BenZbor/My-Projects/CAD Files/SOLIDWORKS/Launcher Assembly.SLDASM

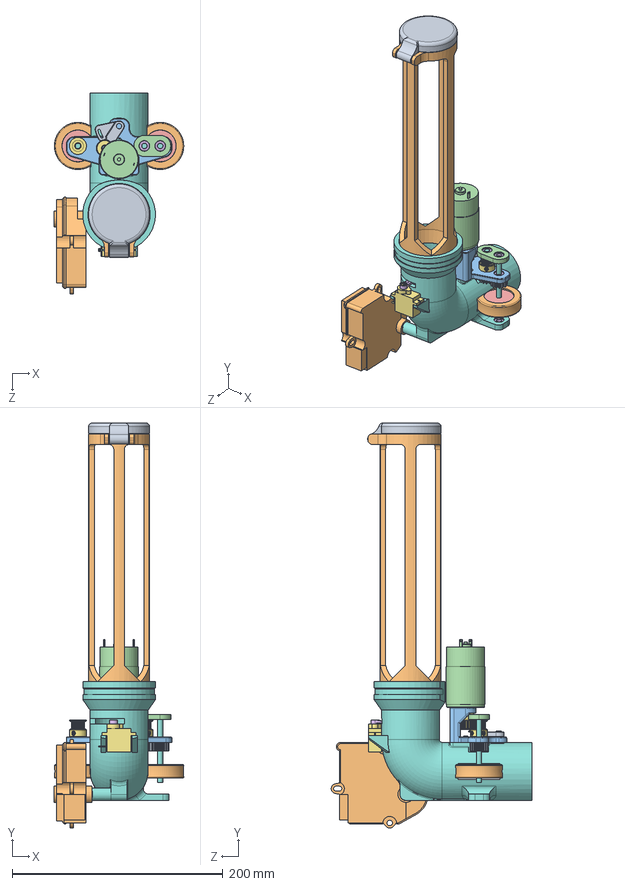
[picture p14: CAD file, 2025-08-28]
CAD Files/SOLIDWORKS/Launcher Assembly.SLDASM
122.8 x 383.9 x 190.2 mm
Magazine
MagazineTop
Feeder
SG90
SG90 Horn
Flywheel x 2
DC Motor
DC Motor Mount
Rotation Motor
Reversing Gear x 2
shaft x 5
GT2_06SWidth_20Num_5IDia_16HDia x 4
Bearing x 7
Coupler
Shaft support
Tensioner rod
Tire x 2
Tensioner V2
