BenZbor/My-Projects/CAD Files/SOLIDWORKS/Shaft support.SLDPRT

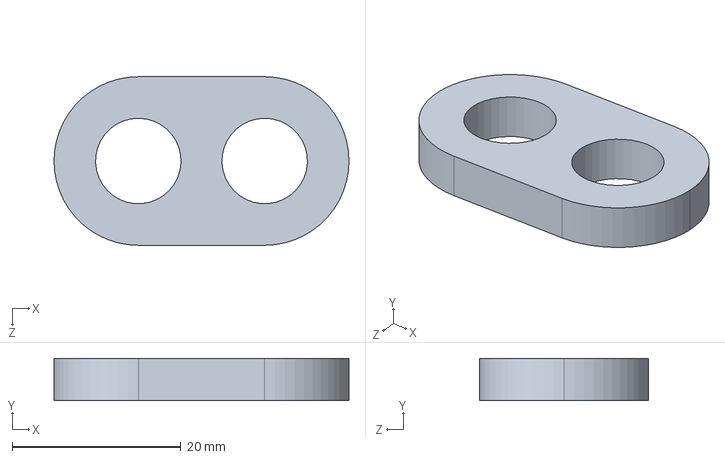
[picture p28: CAD file, 2025-08-28]
CAD Files/SOLIDWORKS/Shaft support.SLDPRT
35.0 x 5.00 x 20.0 mm
