BenZbor/My-Projects/CAD Files/SOLIDWORKS/Tank part/7.4V Battery.SLDPRT

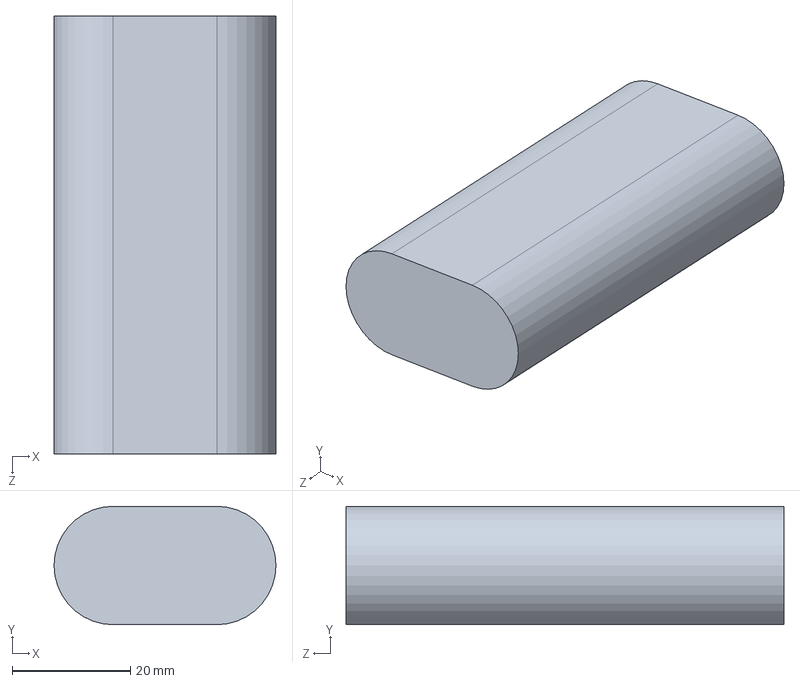
[picture p29: CAD file, 2025-08-28]
CAD Files/SOLIDWORKS/Tank part/7.4V Battery.SLDPRT
37.5 x 20.0 x 74.0 mm
