BenZbor/My-Projects/CAD Files/SOLIDWORKS/shaft.SLDPRT

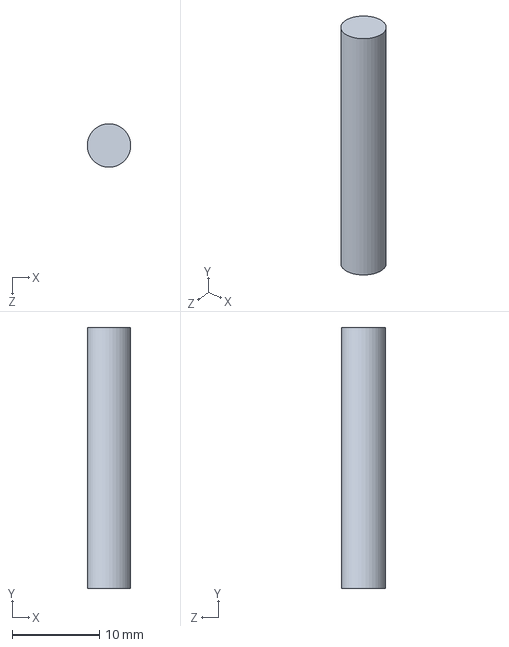
[picture p30: CAD file, 2025-08-28]
CAD Files/SOLIDWORKS/shaft.SLDPRT
4.98 x 30.0 x 5.00 mm
