BenZbor/My-Projects/CAD Files/SOLIDWORKS/Tire.SLDPRT

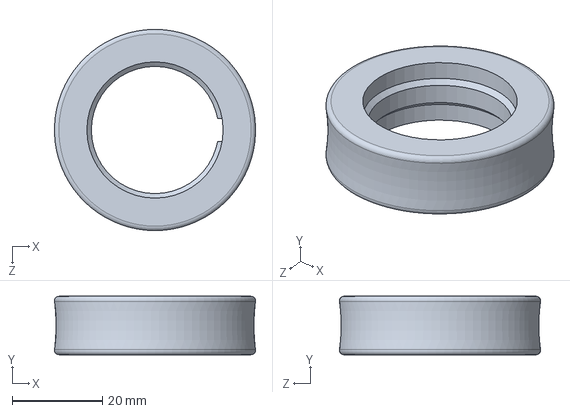
[picture p31: CAD file, 2025-08-28]
CAD Files/SOLIDWORKS/Tire.SLDPRT
44.6 x 13.0 x 44.7 mm
