BenZbor/My-Projects/CAD Files/SOLIDWORKS/Flywheel.SLDPRT

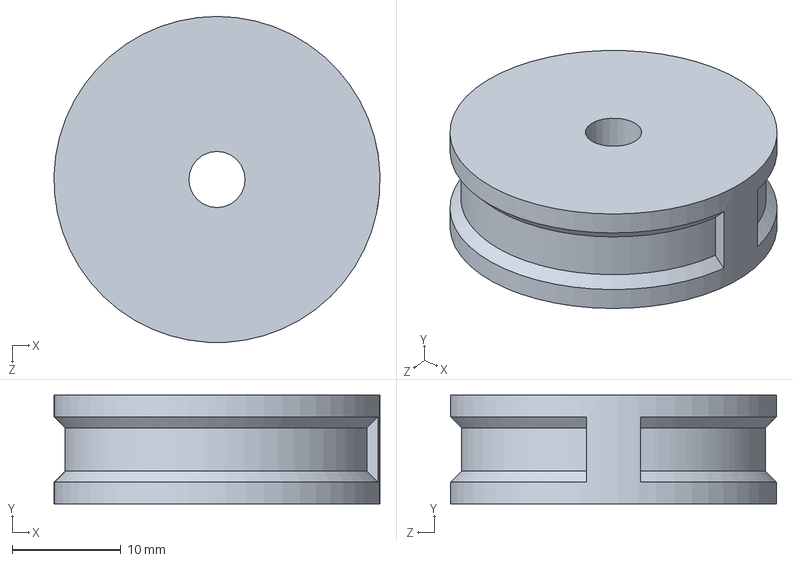
[picture p32: CAD file, 2025-08-28]
CAD Files/SOLIDWORKS/Flywheel.SLDPRT
30.0 x 10.0 x 30.0 mm
