BenZbor/My-Projects/CAD Files/SOLIDWORKS/DC Motor Mount.SLDPRT

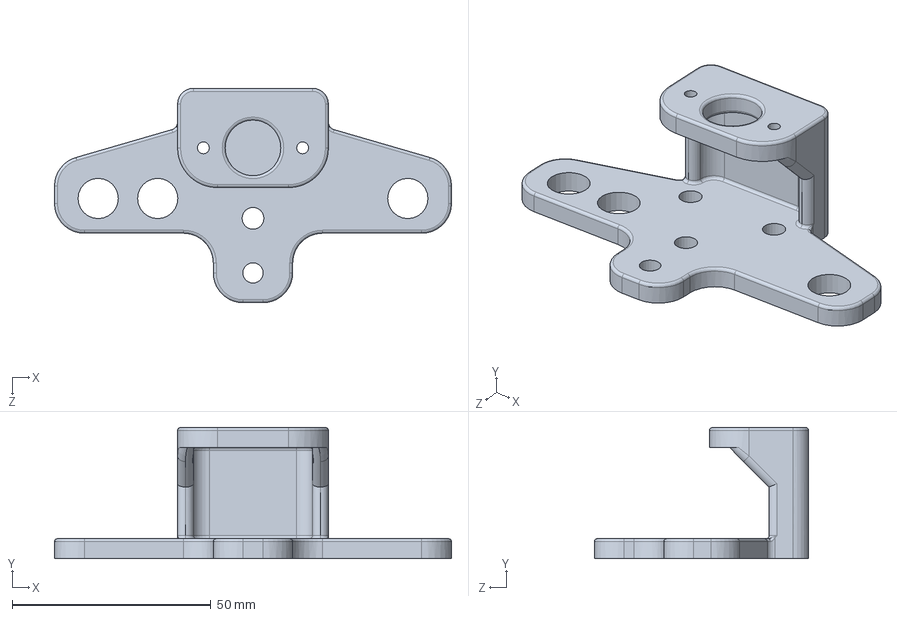
[picture p33: CAD file, 2025-08-28]
CAD Files/SOLIDWORKS/DC Motor Mount.SLDPRT
100.0 x 33.0 x 54.0 mm
