BenZbor/My-Projects/CAD Files/SOLIDWORKS/Feeder.SLDPRT

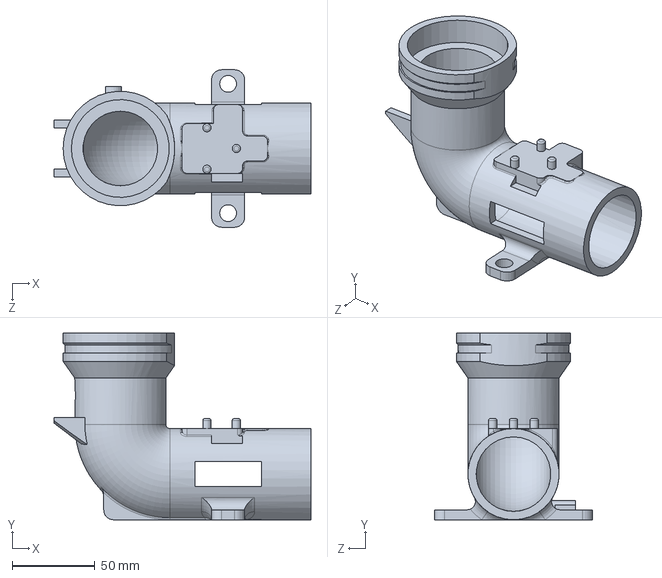
[picture p34: CAD file, 2025-08-28]
CAD Files/SOLIDWORKS/Feeder.SLDPRT
155.0 x 112.5 x 95.0 mm
