BenZbor/My-Projects/CAD Files/SOLIDWORKS/Reversing Gear.SLDPRT

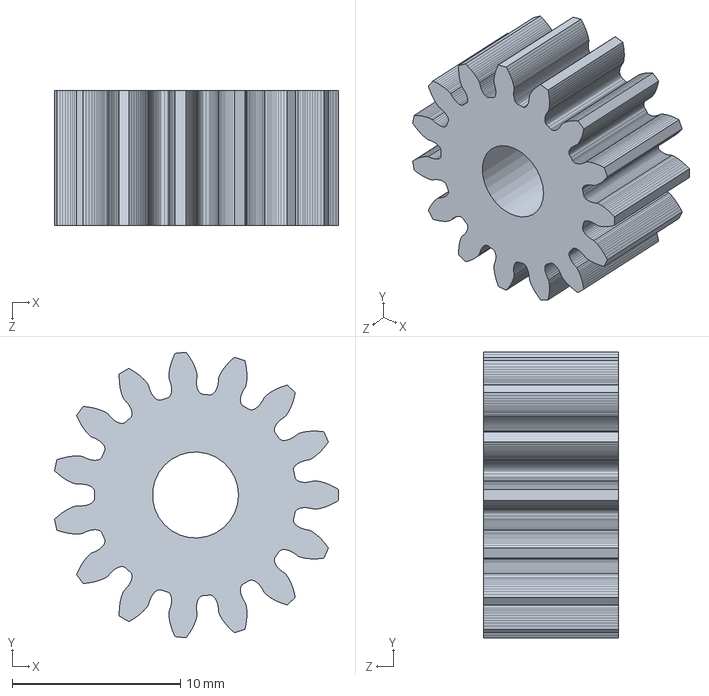
[picture p35: CAD file, 2025-08-28]
CAD Files/SOLIDWORKS/Reversing Gear.SLDPRT
16.9 x 17.0 x 8.00 mm
