BenZbor/My-Projects/CAD Files/SOLIDWORKS/Rotation Motor.SLDPRT

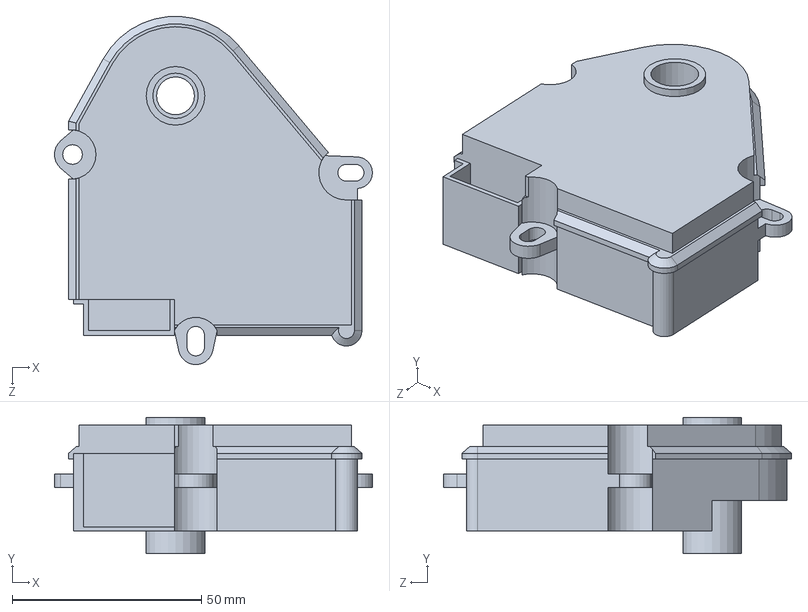
[picture p36: CAD file, 2025-08-28]
CAD Files/SOLIDWORKS/Rotation Motor.SLDPRT
84.0 x 36.0 x 91.9 mm
