BenZbor/My-Projects/CAD Files/SOLIDWORKS/Foam Ball.SLDPRT

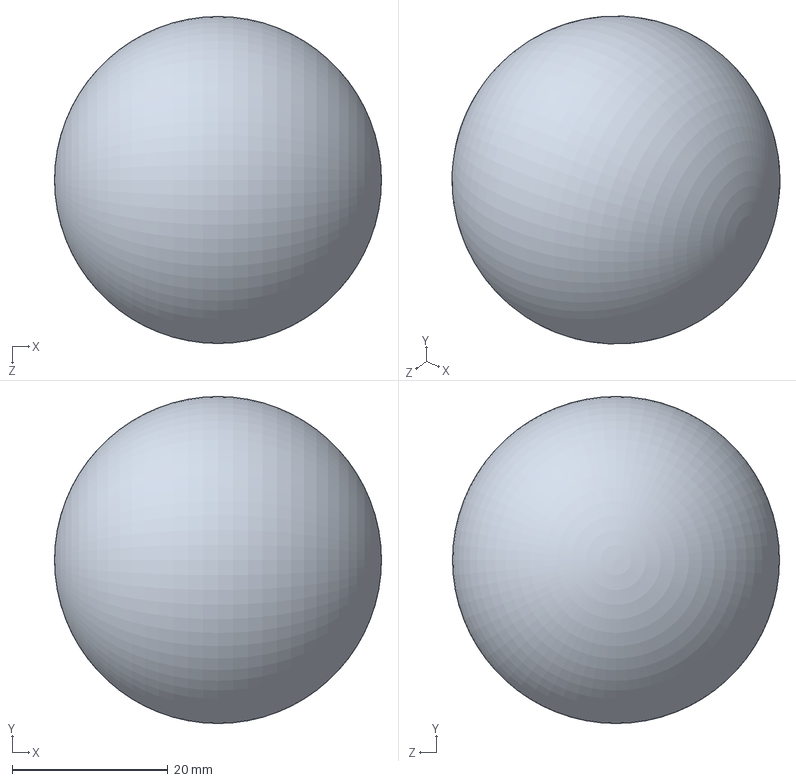
[picture p37: CAD file, 2025-08-28]
CAD Files/SOLIDWORKS/Foam Ball.SLDPRT
42.0 x 42.0 x 42.0 mm
