BenZbor/My-Projects/CAD Files/SOLIDWORKS/Magazine.SLDPRT

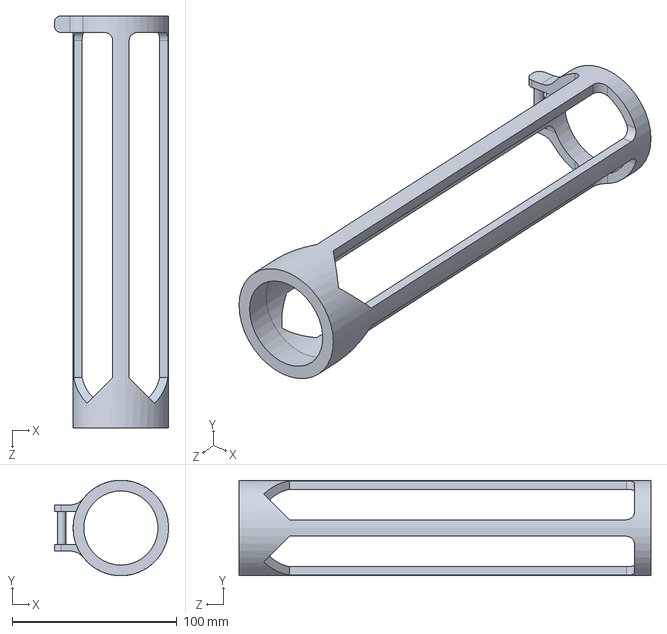
[picture p38: CAD file, 2025-08-28]
CAD Files/SOLIDWORKS/Magazine.SLDPRT
69.4 x 57.8 x 250.0 mm
