BenZbor/My-Projects/CAD Files/SOLIDWORKS/SG90 Horn.SLDPRT

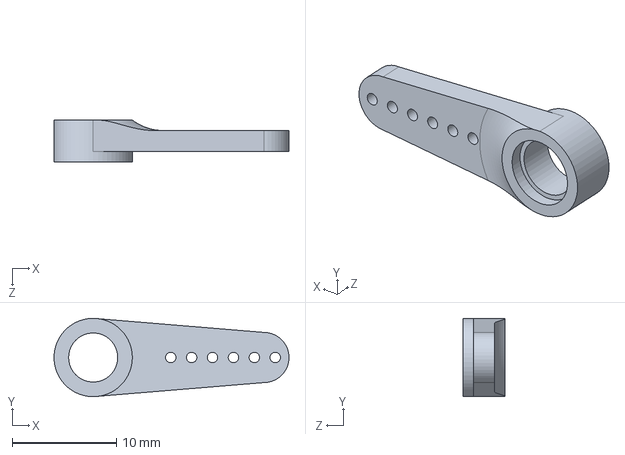
[picture p39: CAD file, 2025-08-28]
CAD Files/SOLIDWORKS/SG90 Horn.SLDPRT
22.5 x 7.50 x 4.00 mm
