BenZbor/My-Projects/CAD Files/SOLIDWORKS/SG90.SLDPRT

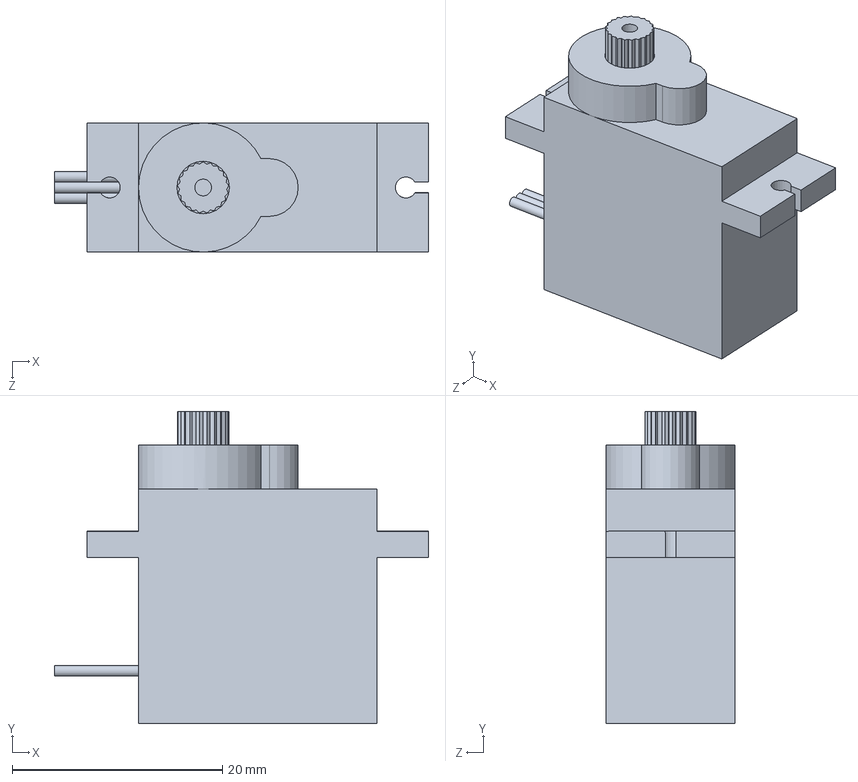
[picture p40: CAD file, 2025-08-28]
CAD Files/SOLIDWORKS/SG90.SLDPRT
35.6 x 29.7 x 12.3 mm
