BenZbor/My-Projects/CAD Files/SOLIDWORKS/Tensioner.SLDPRT

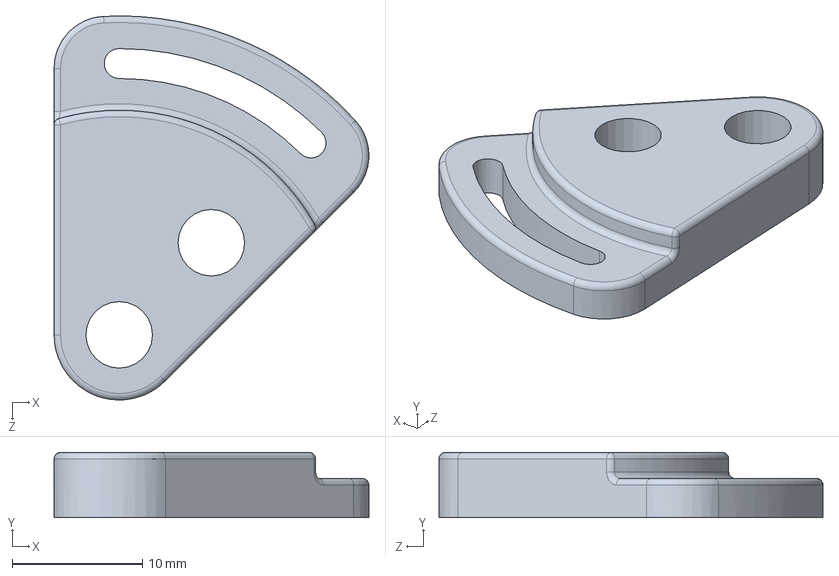
[picture p41: CAD file, 2025-08-28]
CAD Files/SOLIDWORKS/Tensioner.SLDPRT
24.2 x 5.00 x 29.5 mm
