BenZbor/My-Projects/CAD Files/SOLIDWORKS/Bearing.SLDPRT

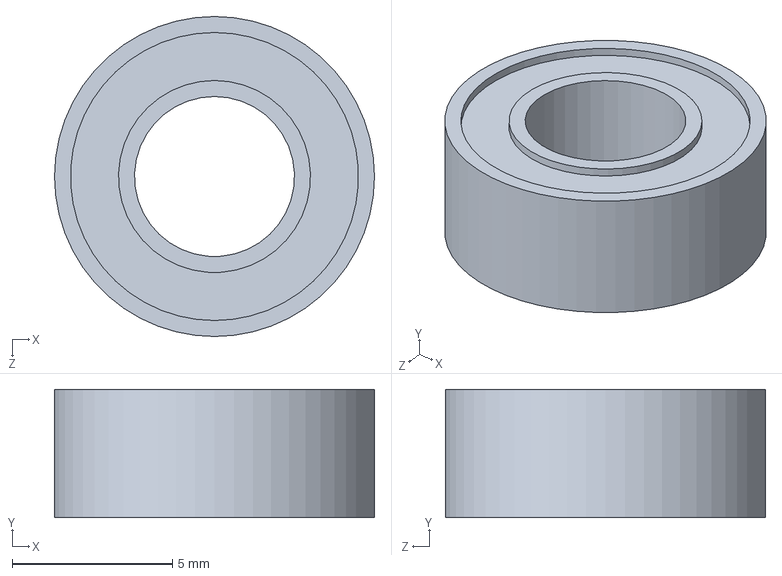
[picture p42: CAD file, 2025-08-28]
CAD Files/SOLIDWORKS/Bearing.SLDPRT
10.0 x 4.00 x 10.0 mm
